BobGlicksman/MN_ACL/Software/Particle_SW/stationfirmware/src/mnutils.cpp

// This file holds common unilities that are used by modules in the RFID project
// of Maker Nexus
//
// (CC BY-NC-SA 3.0 US) 2019 Maker Nexus   https://creativecommons.org/licenses/by-nc-sa/3.0/us/
//

#include "mnutils.h"

enumRetStatus  eRetStatus;

enumAdminCommand g_adminCommand = acIDLE;
String g_adminCommandData = "";

int  eDeviceConfigType;

struct_clientInfo g_clientInfo;
structEEPROMdata EEPROMdata;
struct_stationConfig  g_stationConfig;

String JSONParseError = "";

bool allowDebugToPublish = true;


// instatiate the LCD
LiquidCrystal lcd(A0, A1, A2, A3, D5, D6);

void buzzerBadBeep() {
    tone(BUZZER_PIN,250,500);
}

void buzzerGoodBeepOnce(){
    tone(BUZZER_PIN,750,50); //good
}

void buzzerGoodBeepTwice(){
    tone(BUZZER_PIN,750,50); //good
    delay(100);
    tone(BUZZER_PIN,750,50);
}

void buzzerGoodBeeps3UpDownUp(){
    tone(BUZZER_PIN,1000,50); //good
    delay(100);
    tone(BUZZER_PIN,750,50);
    delay(100);
    tone(BUZZER_PIN,1000,50);
}

// writeToLCD
// pass in "","" to clear screen 
// pass in "" for one line to leave it unchanged
void writeToLCD(String line1, String line2) {
#ifdef LCD_PRESENT
    static String currentLine1 = "";
    static String currentLine2 = "";
    const char* BLANKLINE = "                ";

    if ((line1.length() == 0) & (line2.length() ==0)) {

        lcd.clear();
        currentLine1 = BLANKLINE;
        currentLine2 = BLANKLINE;

    } else {

        String msg = "";
        String msg2 = "";

        if (line1.length() > 0){
            msg = line1;
        } else {
            msg = currentLine1;
        }               
    
        if (line2.length() > 0){
            msg2 = line2;
        } else {
            msg2 = currentLine2;
        }

        lcd.clear();
        lcd.setCursor(0,0);
        lcd.print(msg.substring(0,16)); 
        lcd.setCursor(0,1);
        lcd.print(msg2.substring(0,16));

        currentLine1 = msg; 
        currentLine2 = msg2;
    }

#endif
}


//-------------- Particle Publish Routines --------------
// These routines are used to space out publish events to avoid being throttled.
//

int particlePublish (String eventName, String data) {
    
    static unsigned long lastSentTime = 0;
    
    if (millis() - lastSentTime > 1000 ){
        // only publish once a second
        
        Particle.publish(eventName, data, PRIVATE);
        lastSentTime = millis();
        
        return 0;
        
    } else {
        
        return 1;
        
    }
}


String messageBuffer = "";
// Call this from the main look with a null message
void debugEvent (String message) {

#ifdef DEBUGX_EVENTS_ALLOWED    
    if (message.length() > 0 ){
        // a message was passed in
        
        messageBuffer =  message + " | " + messageBuffer;
        
        if (messageBuffer.length() > 600 ) {
            // message buffer is too long
            
            messageBuffer = messageBuffer.substring(0,570) + " | " + "Some debug messages were truncated";
        }
        
    }
    
    if (messageBuffer.length() > 0) {
        
        // a message buffer is waiting

        if (allowDebugToPublish) {
            
            int rtnCode = particlePublish ("debugX", messageBuffer);
            
            if ( rtnCode == 0 ) {
            
                // it succeeded
                messageBuffer = "";
            
            }
        }
    }
#endif

}



// writes message to a webhook that will send it on to a cloud database
// These have to be throttled to less than one per second on each device
// Parameters:
//    logEvent - a short reason for logging ("checkin","reboot","error", etc)
//    logData - optional freeform text up to 250 characters
//    clientID - optional if this event was for a particular client 
void publishToLogDB (String webhook, String logEvent, String logData, int clientID, String clientFirstName, String clientLastName) {

    const size_t capacity = JSON_OBJECT_SIZE(10);
    DynamicJsonDocument doc(capacity);
    //XXX doc.clear();   // json library says we don't have to do this, but github bug:???

    String idea2 = Time.format(Time.now(), "%F %T");
    doc["dateEventLocal"] = idea2.c_str();
    doc["deviceFunction"] =  g_stationConfig.deviceName.c_str();
    doc["clientID"] = clientID;
    doc["firstName"] = clientFirstName.c_str();
    doc["lastName"] = clientLastName.c_str();
    doc["logEvent"] = logEvent.c_str();
    doc["logData"] = logData.c_str();

    char JSON[2000];
    serializeJson(doc,JSON );
    String publishvalue = String(JSON);

    Particle.publish(webhook, publishvalue, PRIVATE);

    return;

}

void logToDB(String logEvent, String logData, int clientID, String clientFirstName, String clientLastName){
    
    publishToLogDB("RFIDLogging", logEvent, logData, clientID, clientFirstName, clientLastName);

}

void logCheckInOut(String logEvent, String logData, int clientID, String clientFirstName, String clientLastName) {

    publishToLogDB("RFIDLogCheckInOut", logEvent, logData, clientID, clientFirstName, clientLastName);

}

// This is the return called by Particle cloud when the RFIDLogging webhook completes
//
void RFIDLoggingReturn (const char *event, const char *data) {

    debugEvent("called by rfidlogging webhook");

}

// Write to the EEPROM 
//
// 
void EEPROMWrite () {
    int addr = 0;
    EEPROMdata.MN_Identifier = MN_EPROM_ID;
    EEPROM.put(addr, EEPROMdata);
}

// Read from EEPROM
//
//
void EEPROMRead() {
    int addr = 0;
    EEPROM.get(addr,EEPROMdata);
    if (EEPROMdata.MN_Identifier != MN_EPROM_ID) {
        EEPROMdata.deviceType = DEVICETYPE_UNDEFINED;
    }
}


void clearClientInfo() {
    
    g_clientInfo.isValid = false;
    g_clientInfo.isError = false;
    g_clientInfo.lastName = "";
    g_clientInfo.firstName = "";
    g_clientInfo.clientID = 0;
    g_clientInfo.RFIDCardKey = "";
    g_clientInfo.contractStatus = "";
    g_clientInfo.memberNumber = "";
    g_clientInfo.amountDue = 0;
    
}

// ----------------- setStationConfig ----------
//
//  setStationConfig
//
void setStationConfig(int deviceType, String deviceName, String LCDName, String logEvent, String photoDisplay, String OKKeywords) {

    g_stationConfig.deviceType = deviceType;
    g_stationConfig.deviceName = deviceName;
    g_stationConfig.LCDName = LCDName;
    g_stationConfig.logEvent = logEvent;
    g_stationConfig.photoDisplay = photoDisplay;
    g_stationConfig.OKKeywords = OKKeywords;
    g_stationConfig.isValid = true;

}
